MrBlinky/avr-hvsp/images/12v-dc-dc-converter-with-enable.jpg

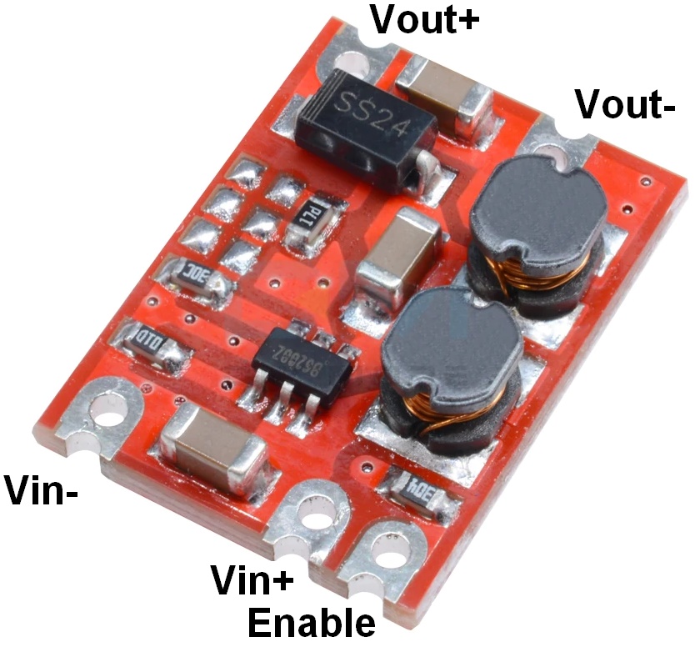
images/12v-dc-dc-converter-with-enable.jpg
