MrBlinky/avr-hvsp/images/prototype.jpg

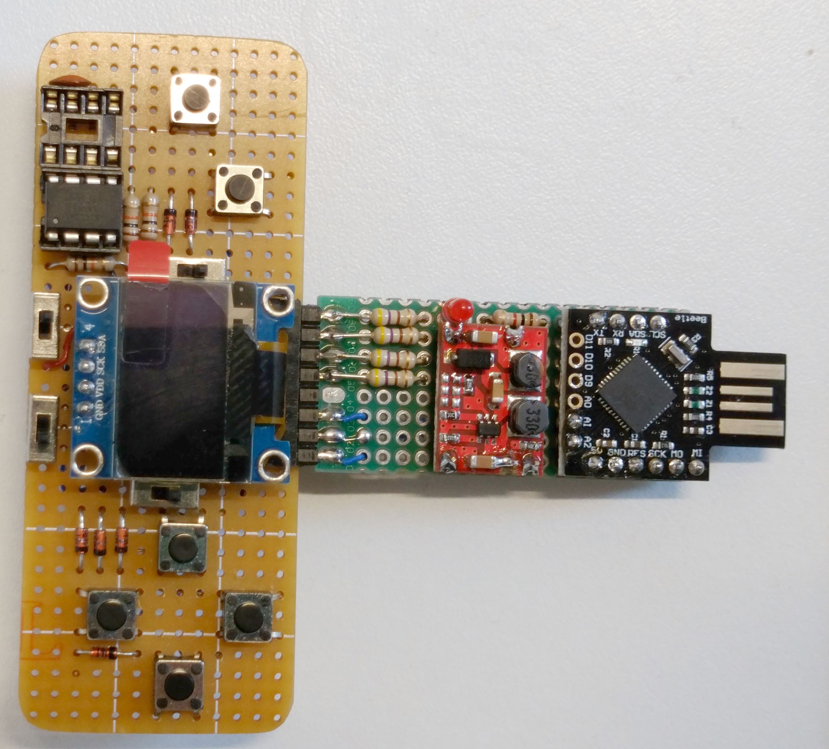
images/prototype.jpg
