MrBlinky/avr-hvsp/images/2-assembled-half.jpg

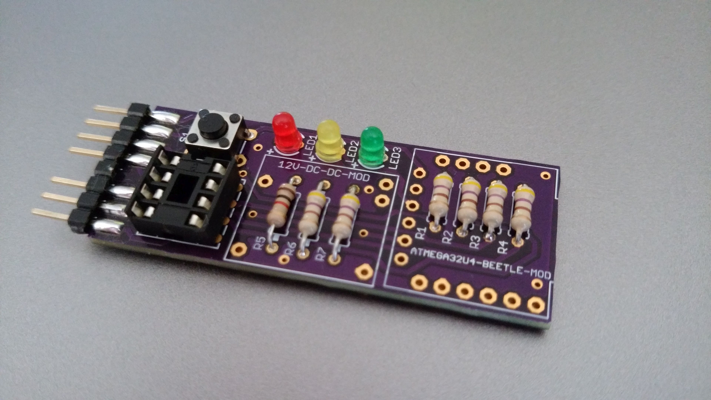
images/2-assembled-half.jpg
