MrBlinky/avr-hvsp/images/4-assembled-bottom.jpg

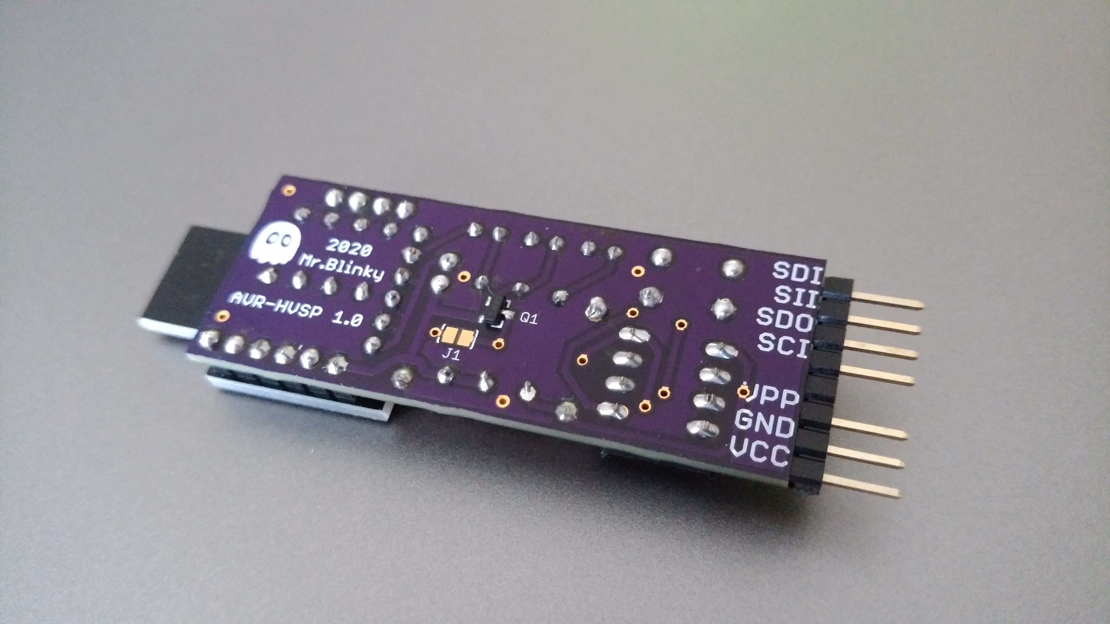
images/4-assembled-bottom.jpg
