MrBlinky/avr-hvsp/images/prototype-wiring.png

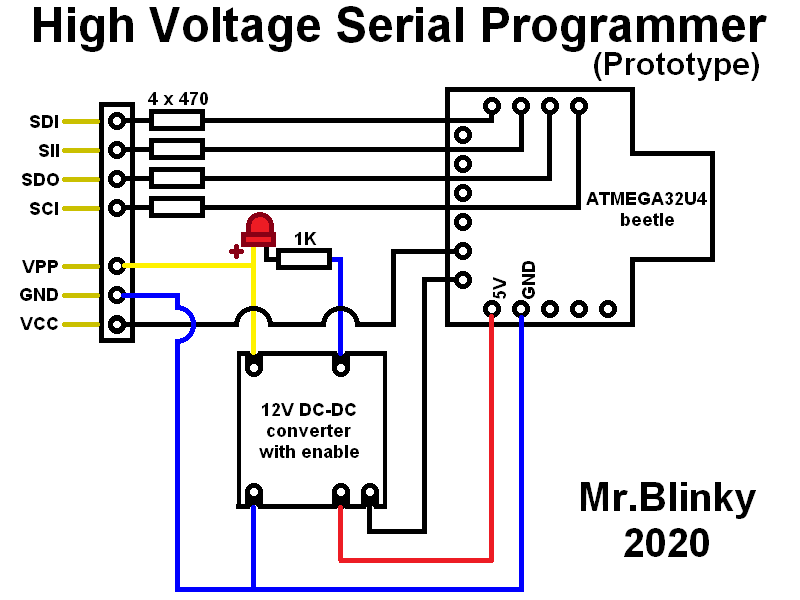
images/prototype-wiring.png
